Kampi/Extension-HW/production/extension-CHECKED/HTML/images/cat_pdf_schematic_ZSWatch-Extension-schematic.png

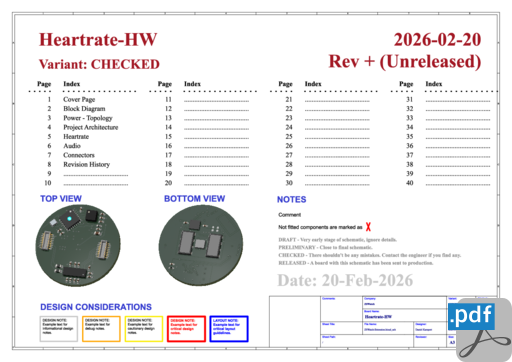
production/extension-CHECKED/HTML/images/cat_pdf_schematic_ZSWatch-Extension-schematic.png
