Kampi/Extension-HW/production/extension-CHECKED/HTML/images/cat_png_3d_viewer_angled_bottom_ZSWatch-Extension-angled_bottom.png

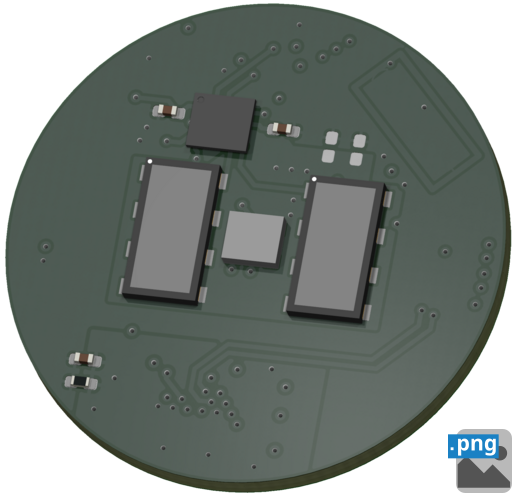
production/extension-CHECKED/HTML/images/cat_png_3d_viewer_angled_bottom_ZSWatch-Extension-angled_bottom.png
