Kampi/Extension-HW/production/extension-CHECKED/HTML/images/cat_png_3d_viewer_bottom_ZSWatch-Extension-bottom.png

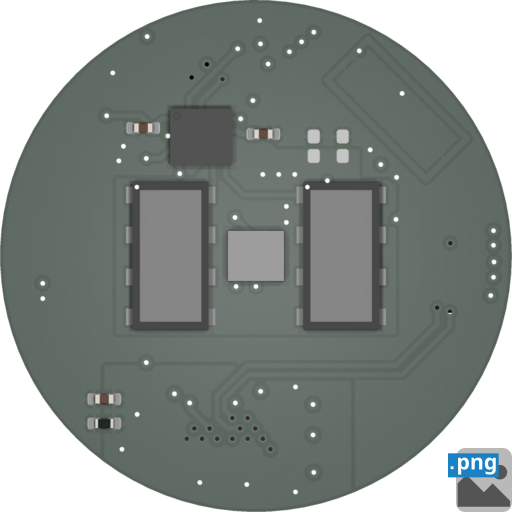
production/extension-CHECKED/HTML/images/cat_png_3d_viewer_bottom_ZSWatch-Extension-bottom.png
