Kampi/Extension-HW/production/extension-CHECKED/Images/ZSWatch-Extension-angled_top.png

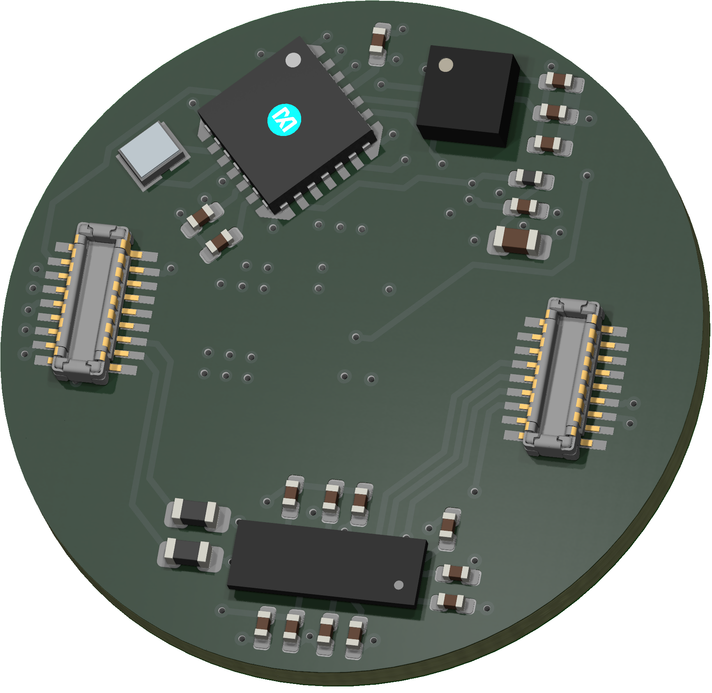
production/extension-CHECKED/Images/ZSWatch-Extension-angled_top.png
