Kampi/Extension-HW/production/extension-CHECKED/HTML/images/cat_pdf_fabrication_ZSWatch-Extension-fabrication.png

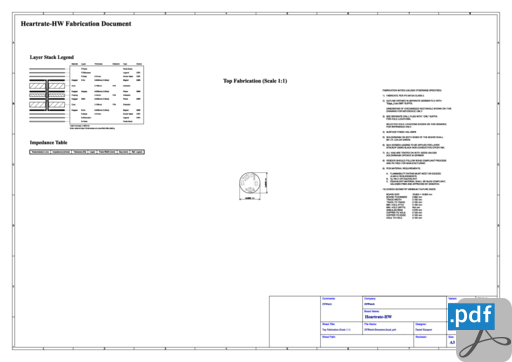
production/extension-CHECKED/HTML/images/cat_pdf_fabrication_ZSWatch-Extension-fabrication.png
